sherwin-sattar/clock-sensor/Web_UI/img/—Pngtree—computer themed circuit board vector_15255444.jpg

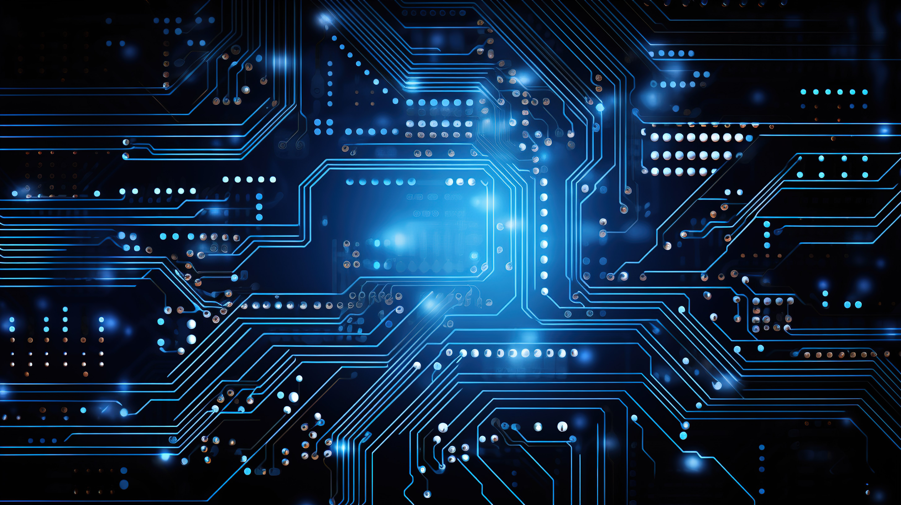
Web_UI/img/—Pngtree—computer themed circuit board vector_15255444.jpg
