sherwin-sattar/clock-sensor/Web_UI/img/—Pngtree—digitalized blockchain cube exploring the_13503684.jpg

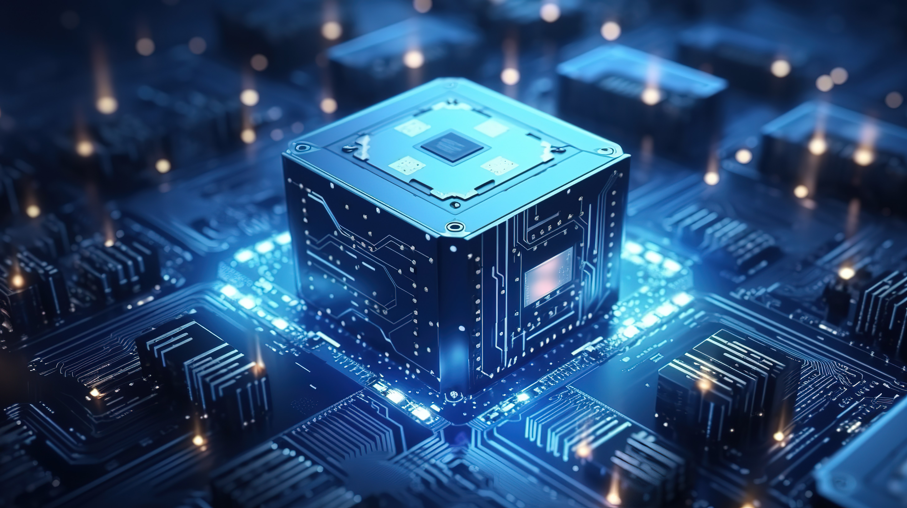
Web_UI/img/—Pngtree—digitalized blockchain cube exploring the_13503684.jpg
